Mindar/RundtischNC/img/display-widerstände2.jpg

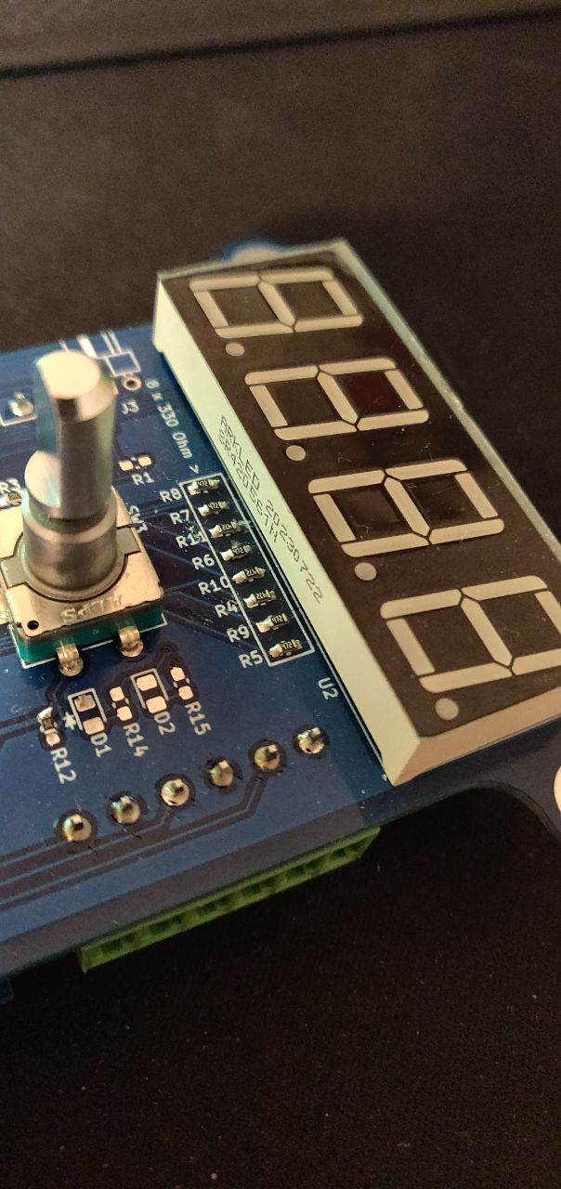
img/display-widerstände2.jpg
