Mindar/RundtischNC/img/img1.jpg

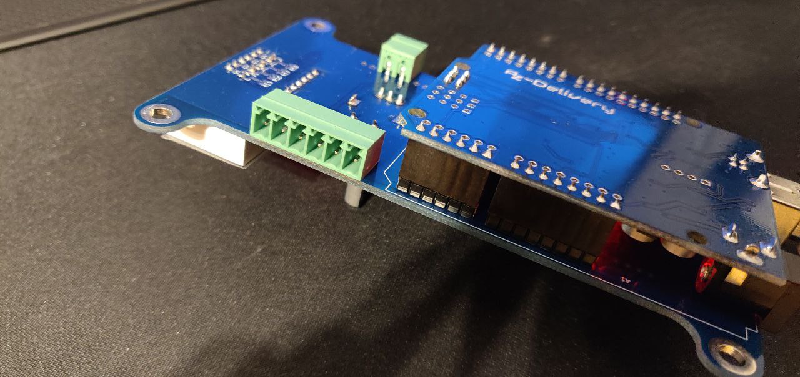
img/img1.jpg
