Mindar/RundtischNC/img/img2.jpg

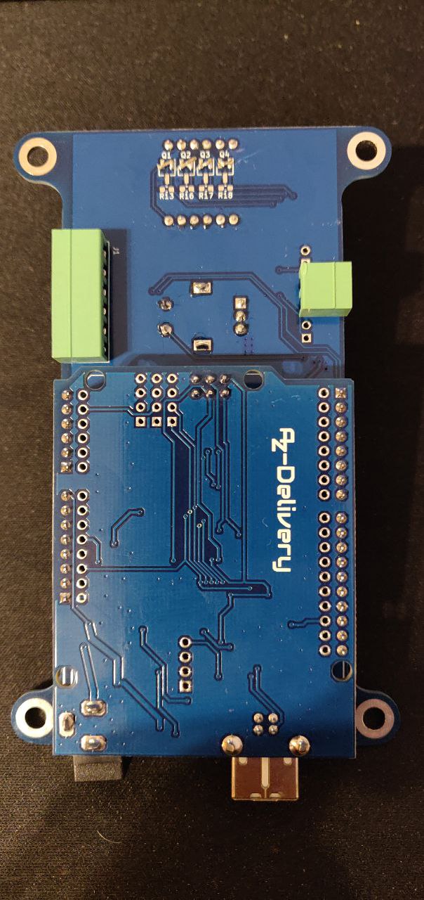
img/img2.jpg
