Mindar/RundtischNC/img/img4.jpg

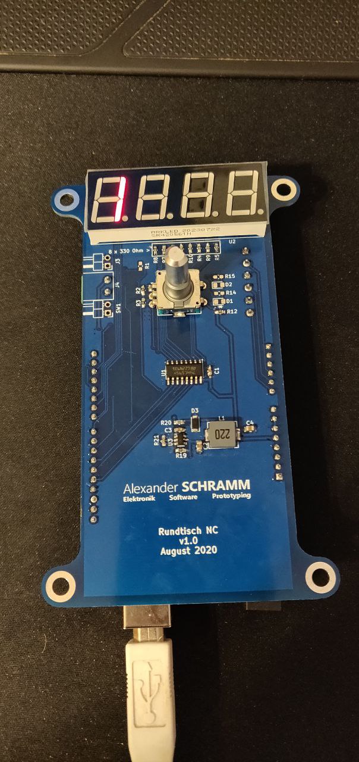
img/img4.jpg
