Mindar/RundtischNC/img/img6.jpg

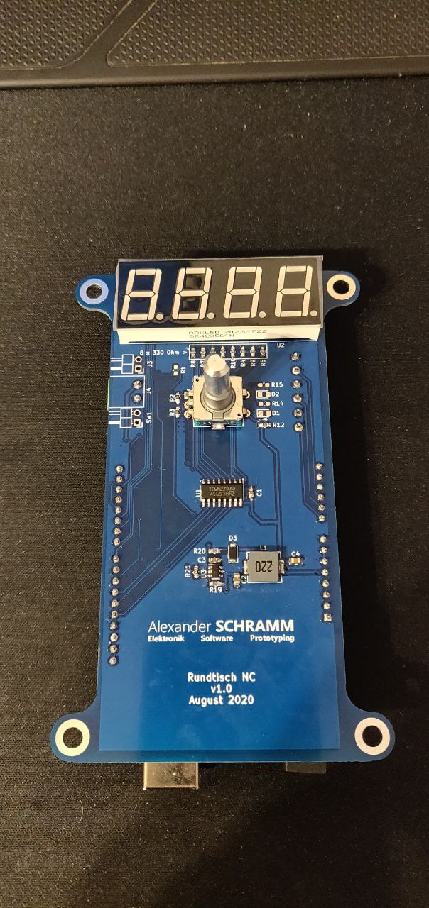
img/img6.jpg
