Mindar/RundtischNC/img/img9.jpg

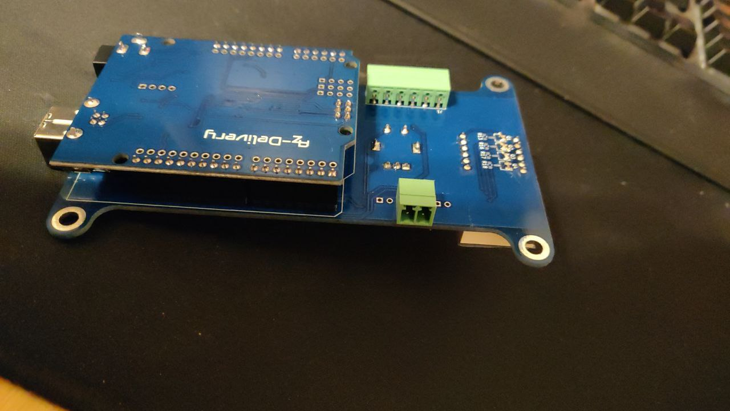
img/img9.jpg
